ovonpape/esphome_universal-remote/hardware/PCB/PDF/hassbeam_etch_silk_bottom.pdf

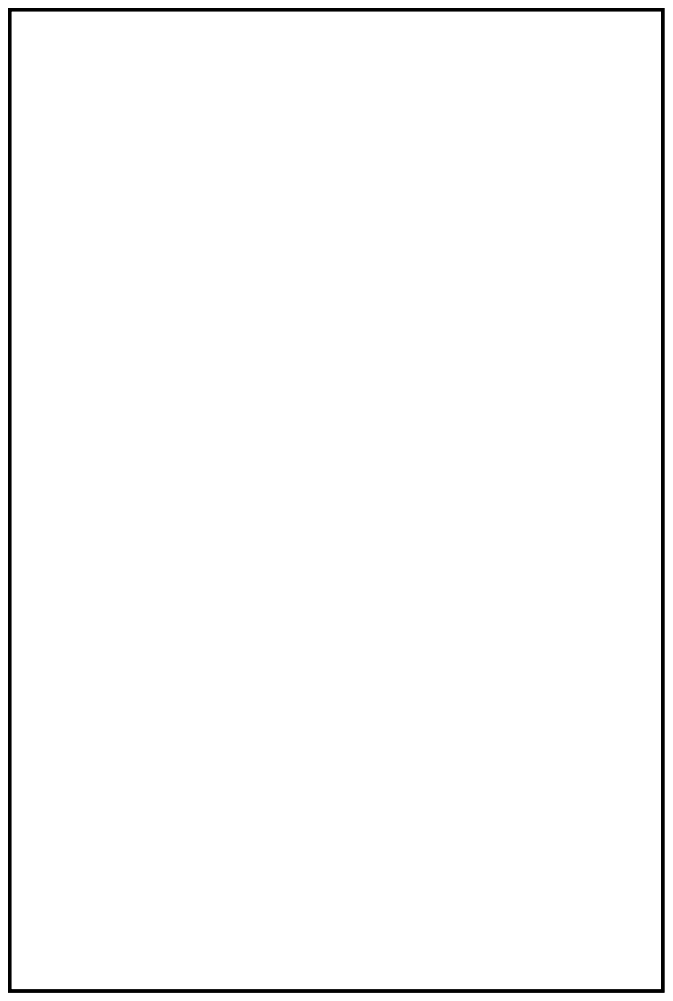
[picture p19: page 1]
