ovonpape/esphome_universal-remote/hardware/PCB/PDF/hassbeam_etch_silk_bottom_mirror.pdf

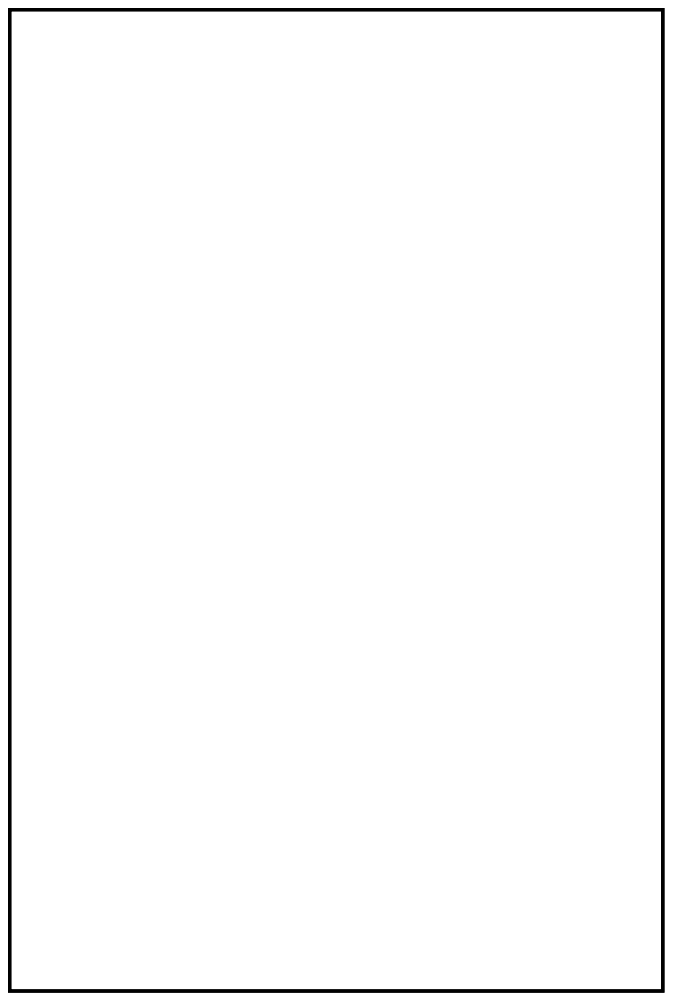
[picture p20: page 1]
