ovonpape/esphome_universal-remote/hardware/PCB/PDF/hassbeam_etch_silk_top.pdf

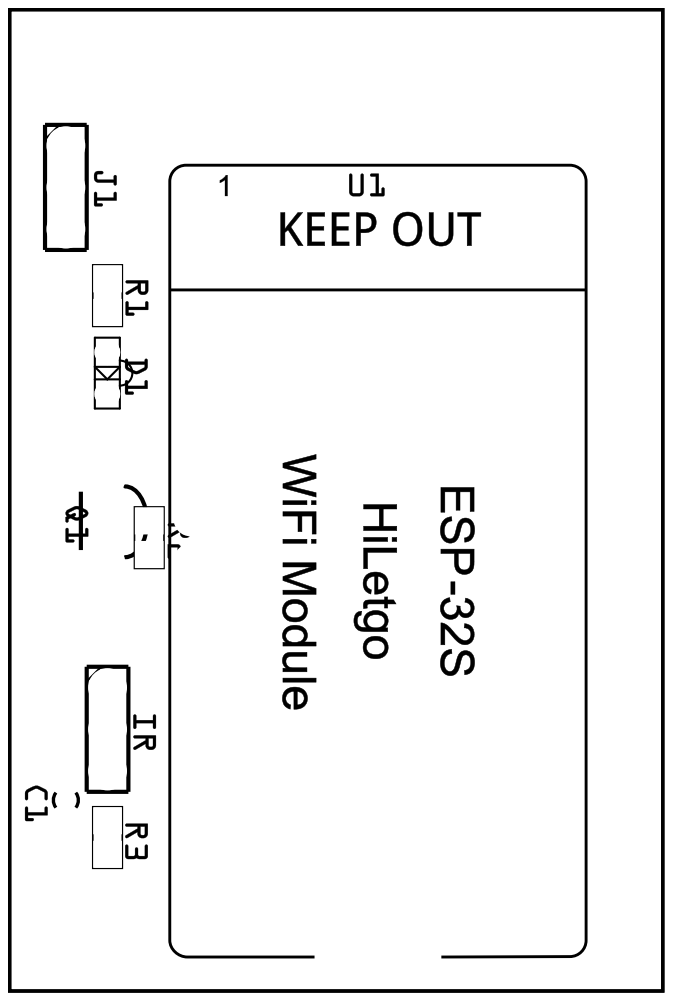
[picture p21: page 1]
