ovonpape/esphome_universal-remote/hardware/PCB/PDF/hassbeam_etch_silk_top_mirror.pdf

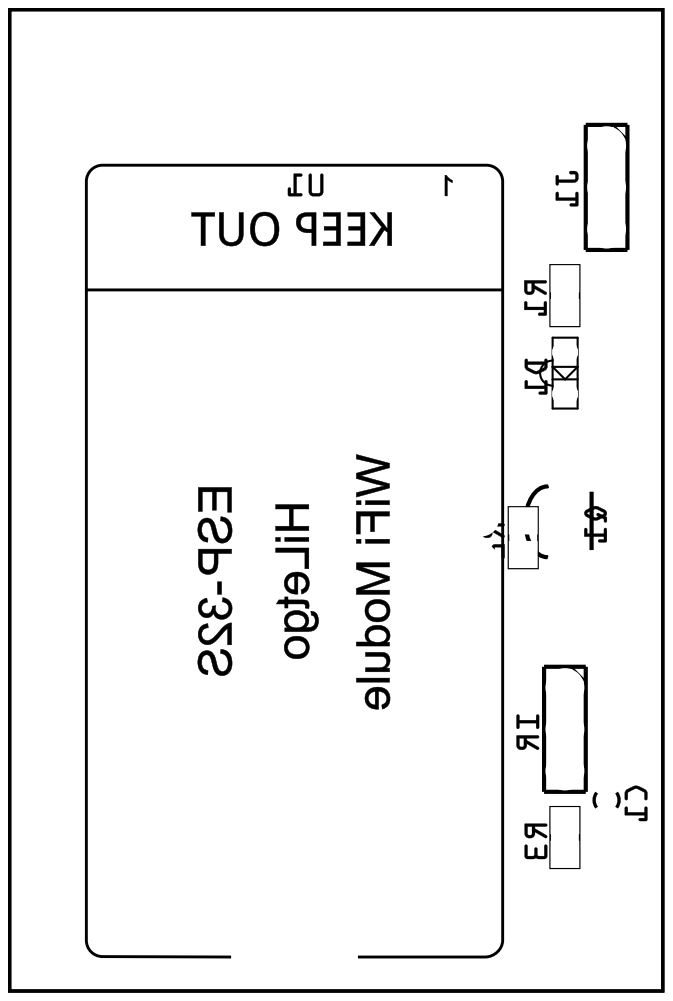
[picture p22: page 1]
